Linoprit/ThetaMon3/Doc/Ressources/IMG_20240623_202408.jpg

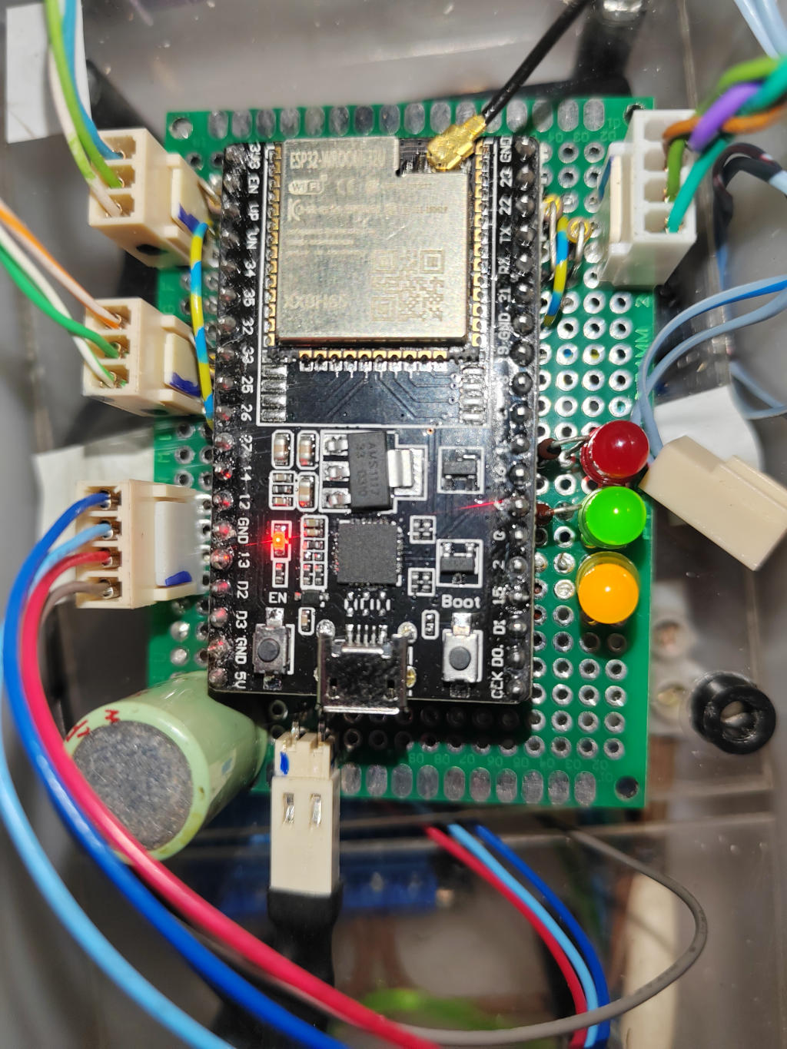
Doc/Ressources/IMG_20240623_202408.jpg
