Linoprit/ThetaMon3/Doc/Ressources/IMG_20240629_132339.jpg

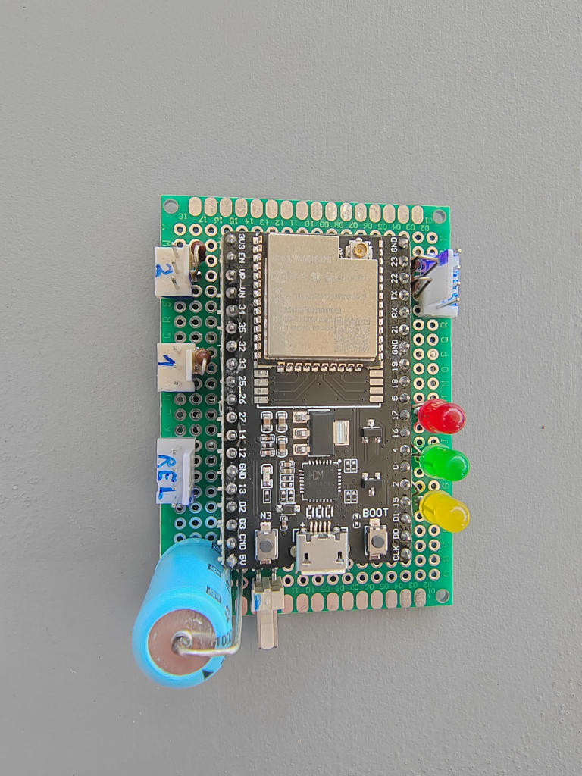
Doc/Ressources/IMG_20240629_132339.jpg
