Linoprit/ThetaMon3/Doc/Ressources/IMG_20240629_132347.jpg

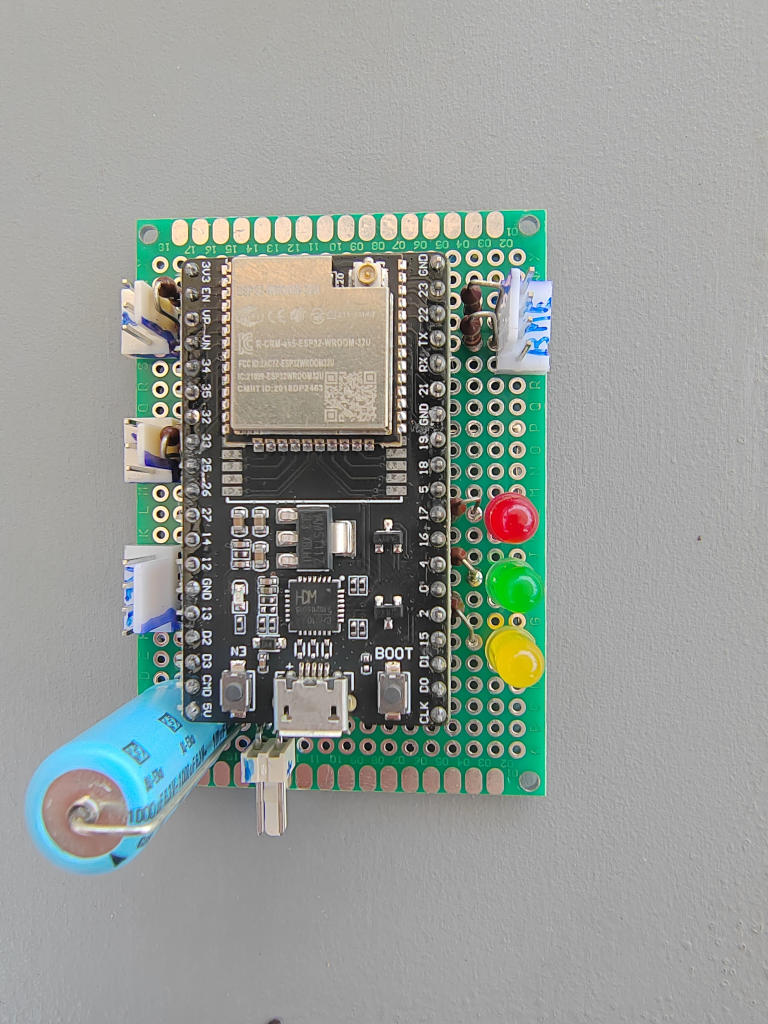
Doc/Ressources/IMG_20240629_132347.jpg
