Linoprit/ThetaMon3/Doc/Ressources/IMG_20240629_132409.jpg

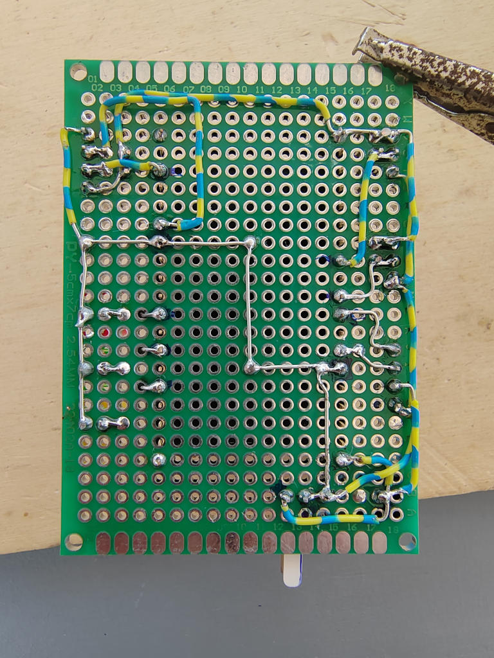
Doc/Ressources/IMG_20240629_132409.jpg
