Linoprit/ThetaMon3/Doc/Ressources/IMG_20240629_132420.jpg

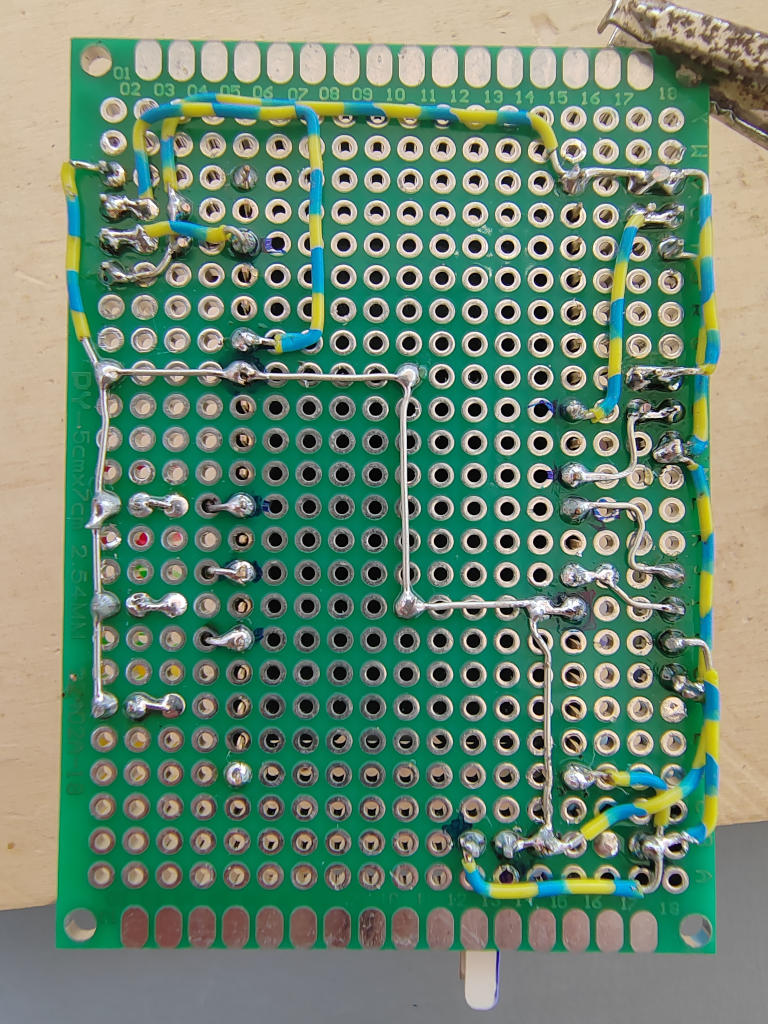
Doc/Ressources/IMG_20240629_132420.jpg
