Linoprit/ThetaMon3/Doc/Ressources/IMG_20240830_092953.jpg

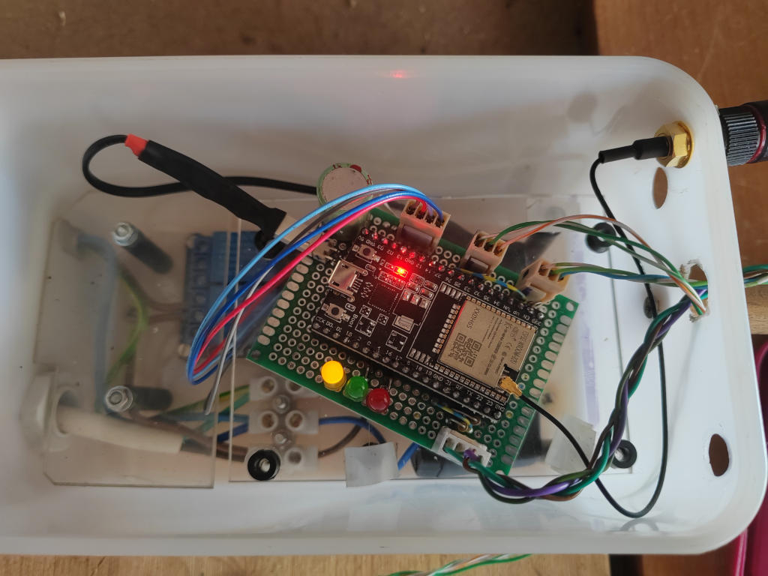
Doc/Ressources/IMG_20240830_092953.jpg
