Linoprit/ThetaMon3/Doc/Ressources/IMG_20240830_093123.jpg

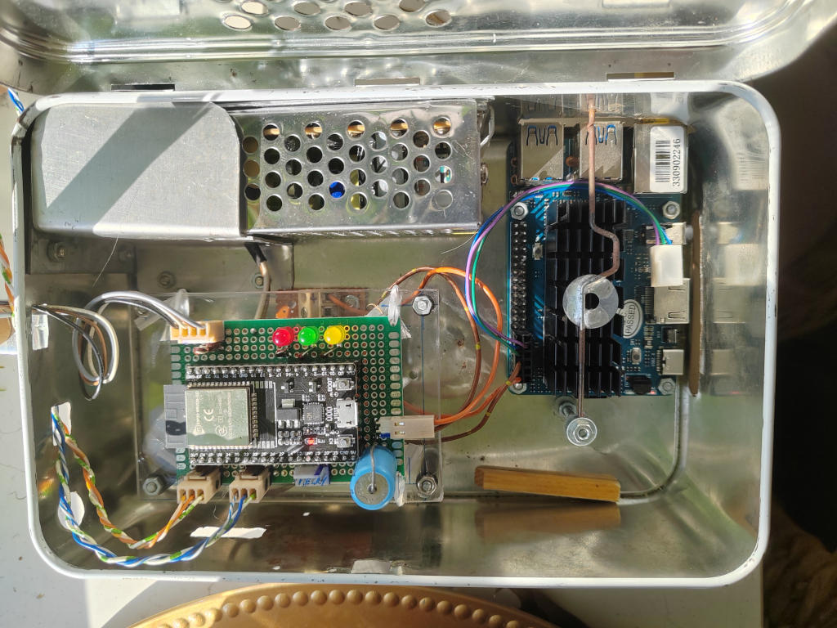
Doc/Ressources/IMG_20240830_093123.jpg
